yardenmorag/robotic-arm/SImulation/URDF_mesh3/meshes/link_1.STL

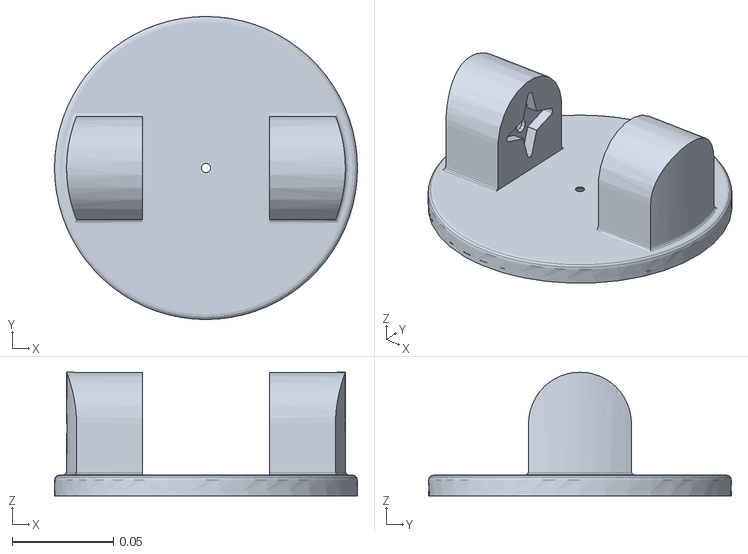
[picture p13: CAD file, 2026-06-02]
SImulation/URDF_mesh3/meshes/link_1.STL
0.149 x 0.149 x 0.0609
