yardenmorag/robotic-arm/SImulation/URDF_mesh3/meshes/link_5.STL

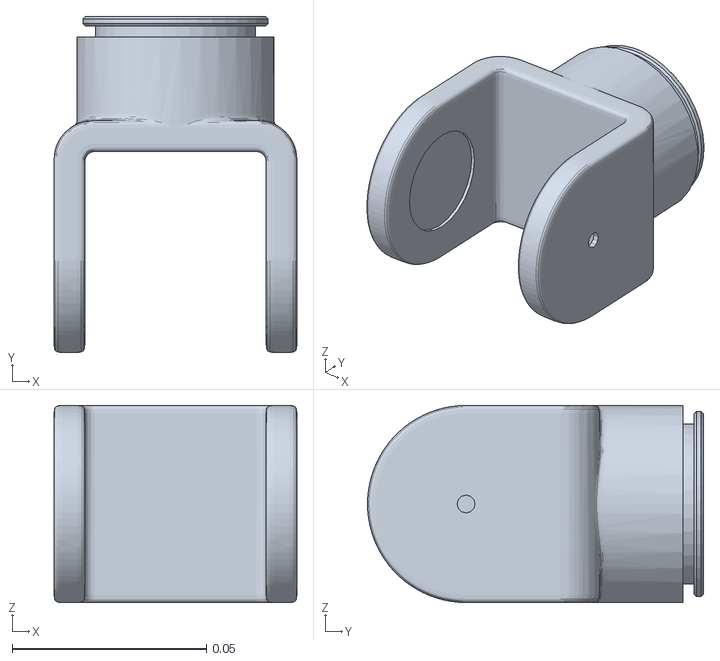
[picture p14: CAD file, 2026-06-02]
SImulation/URDF_mesh3/meshes/link_5.STL
0.0625 x 0.0865 x 0.0507
