yardenmorag/robotic-arm/SImulation/URDF_mesh3/meshes/link_3.STL

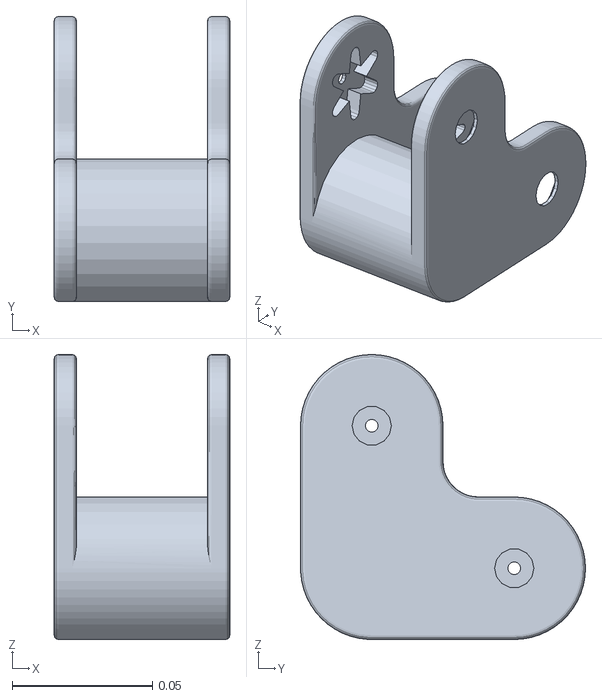
[picture p15: CAD file, 2026-06-02]
SImulation/URDF_mesh3/meshes/link_3.STL
0.0625 x 0.102 x 0.101
